atbrask/RPIWeather/Pictures/433MHzReceiverBottom.jpg

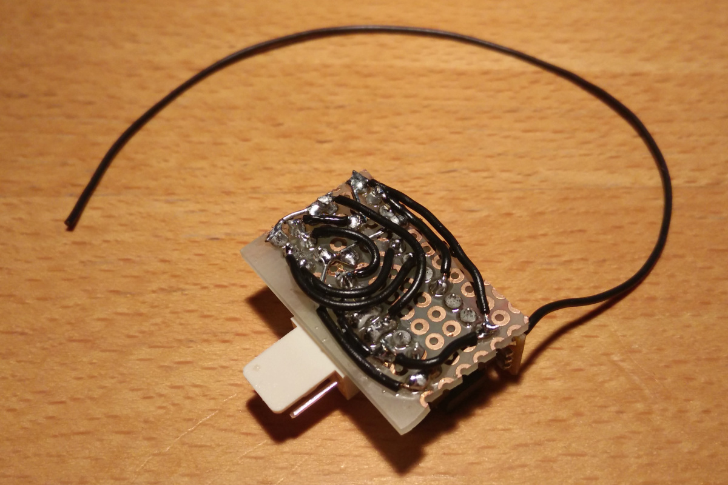
Pictures/433MHzReceiverBottom.jpg
