atbrask/RPIWeather/Pictures/finished boards.jpg

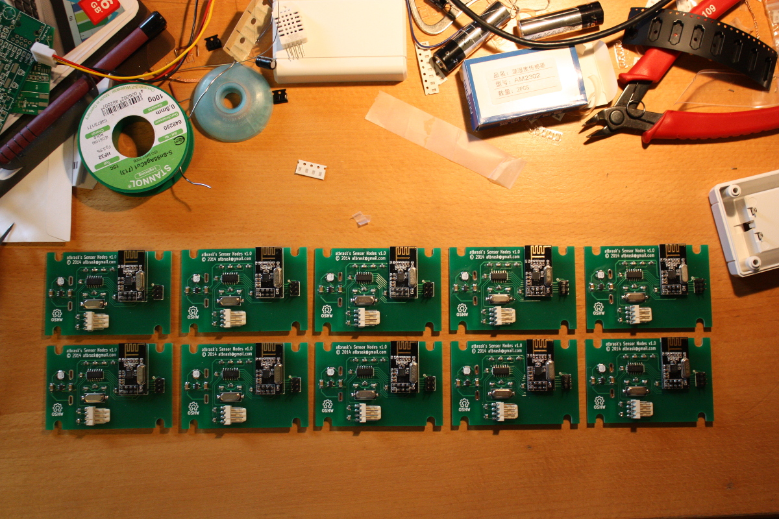
Pictures/finished boards.jpg
