atbrask/RPIWeather/Pictures/node back.jpg

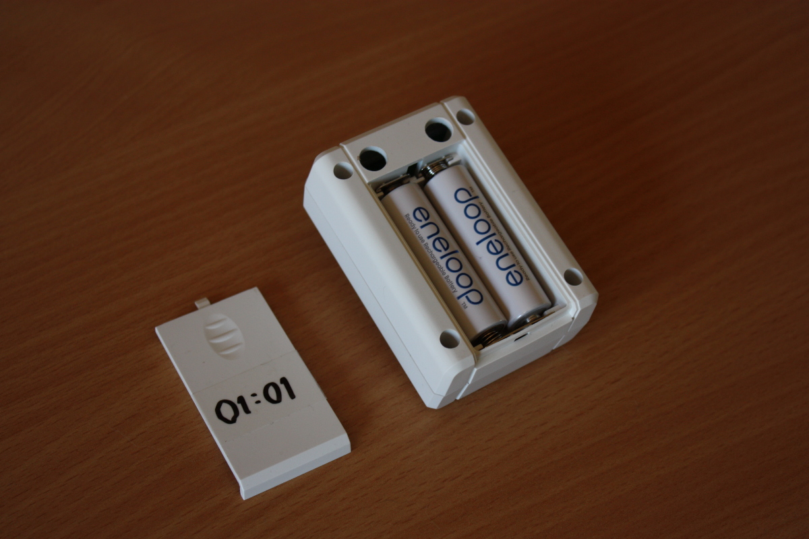
Pictures/node back.jpg
