atbrask/RPIWeather/Pictures/node front.jpg

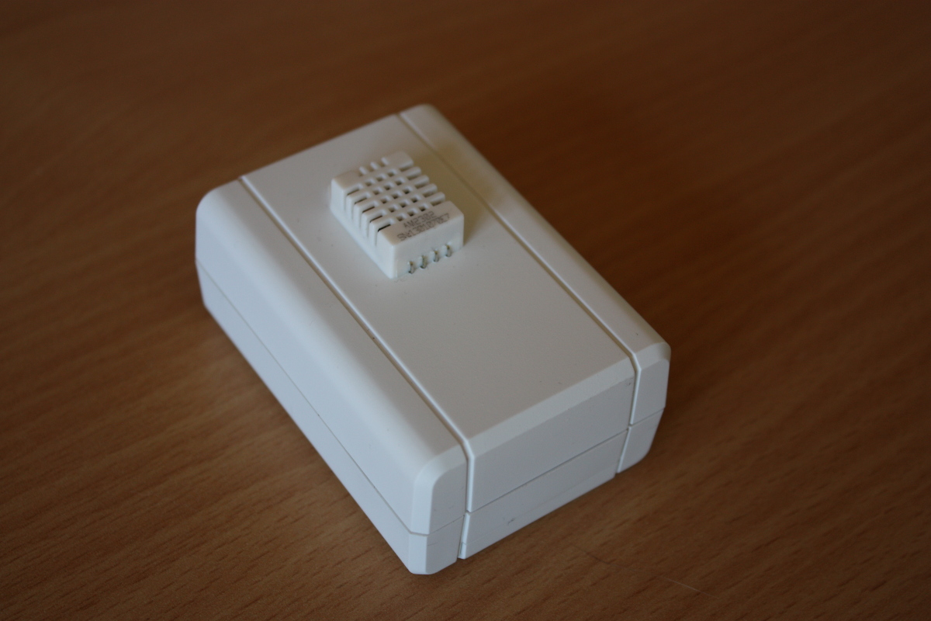
Pictures/node front.jpg
