atbrask/RPIWeather/Pictures/nodes front.jpg

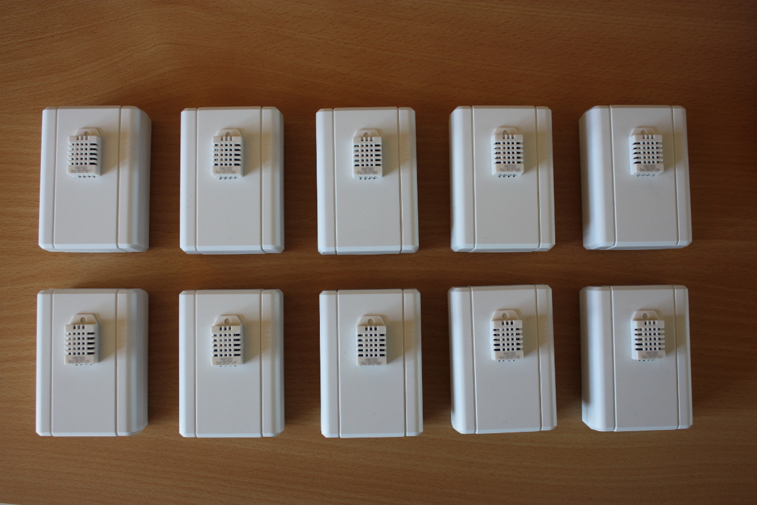
Pictures/nodes front.jpg
