atbrask/RPIWeather/SensorNodes/Hardware/SensorNode.sch

## KiCad design SensorNodes/Hardware/SensorNode.sch (2014-07-30)

Schematic: SensorNode.sch

Parts:
BT1: BATTERY
C1, C2: 10uF
C3, C4, C7, C8, C9: 100nF
C5, C6: 22pF
IC1: ATTINY84A-SS; SO14
L1: 10uH
P1: DHT22
P2: ICSP
P3: nRF24L01
R1, R3: 10k
R2, R4: 1M
U1: TPS61097
X1: 8MHz (18pF)

Notes on the sheet:
Sensor node based on ATTINY84 and nRF24L01
